jareddilley/LED-Settlers-of-Catan-V2/STL files/Decals/Boat.stl

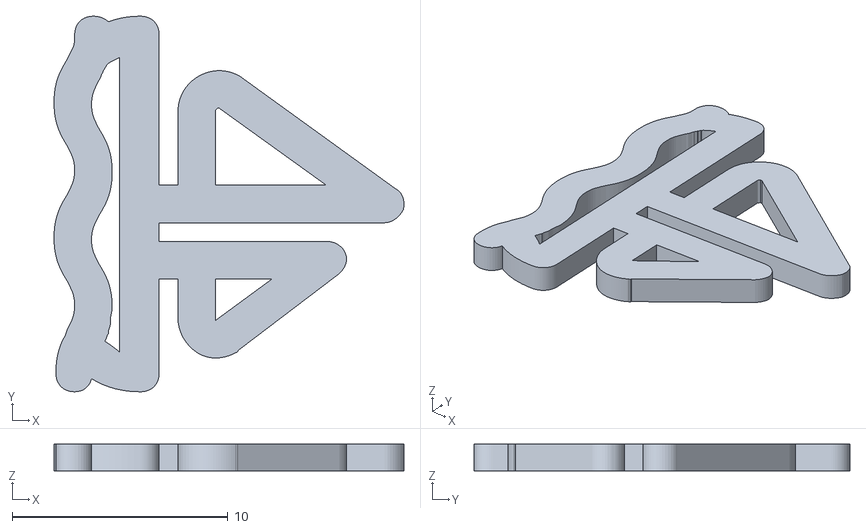
[picture p20: CAD file, 2024-02-23]
STL files/Decals/Boat.stl
16.2 x 17.4 x 1.25
