jareddilley/LED-Settlers-of-Catan-V2/STL files/Boarders/cover-other.stl

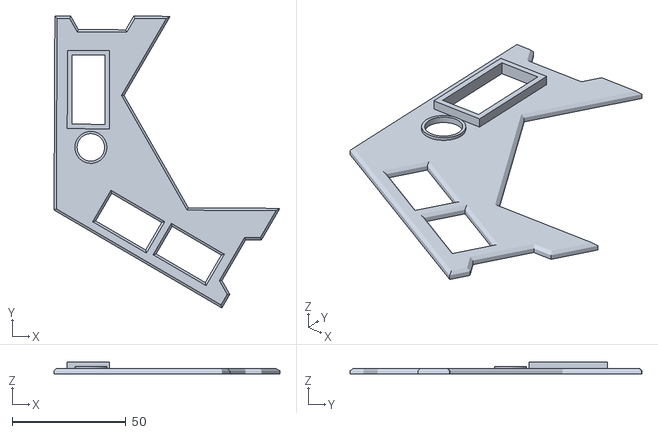
[picture p21: CAD file, 2024-02-23]
STL files/Boarders/cover-other.stl
99.6 x 128.6 x 5.50
