jareddilley/LED-Settlers-of-Catan-V2/STL files/Decals/wheat (1).stl

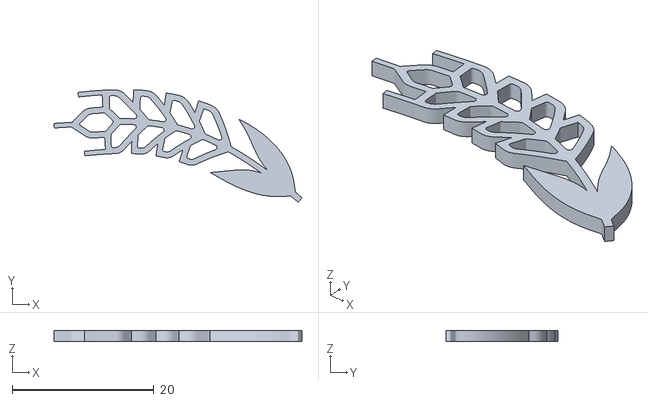
[picture p22: CAD file, 2024-02-23]
STL files/Decals/wheat (1).stl
35.1 x 15.9 x 1.50
