jareddilley/LED-Settlers-of-Catan-V2/STL files/Decals/Port-Diffuser.stl

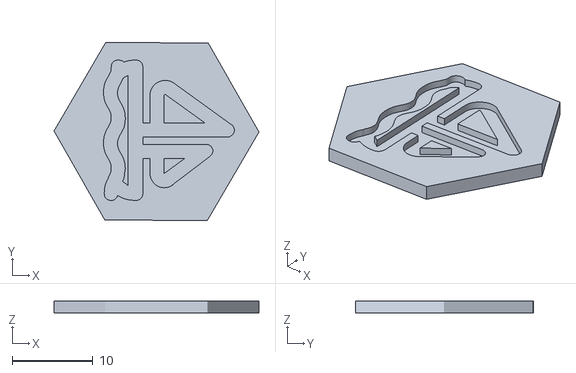
[picture p23: CAD file, 2024-02-23]
STL files/Decals/Port-Diffuser.stl
25.4 x 22.1 x 1.50
