jareddilley/LED-Settlers-of-Catan-V2/STL files/Main Board/1.stl

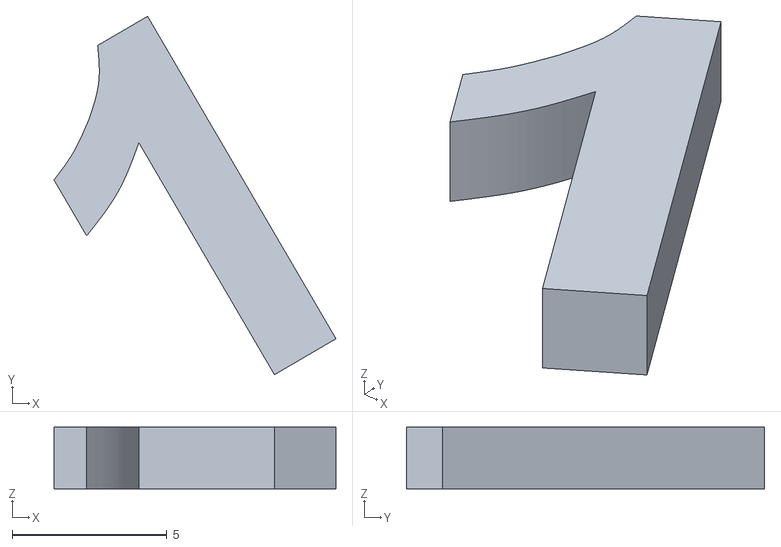
[picture p24: CAD file, 2024-02-23]
STL files/Main Board/1.stl
9.10 x 11.6 x 2.00
