jareddilley/LED-Settlers-of-Catan-V2/STL files/Decals/f.stl

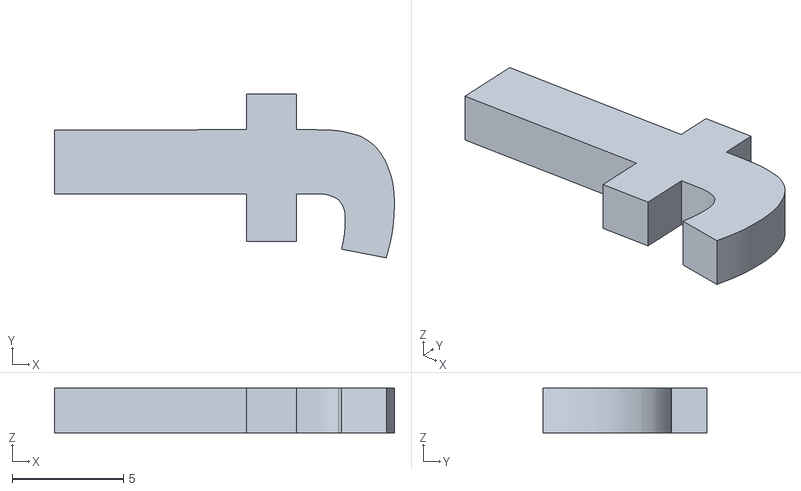
[picture p25: CAD file, 2024-02-23]
STL files/Decals/f.stl
15.3 x 7.35 x 2.00
