jareddilley/LED-Settlers-of-Catan-V2/STL files/Main Board/2-Dot.stl

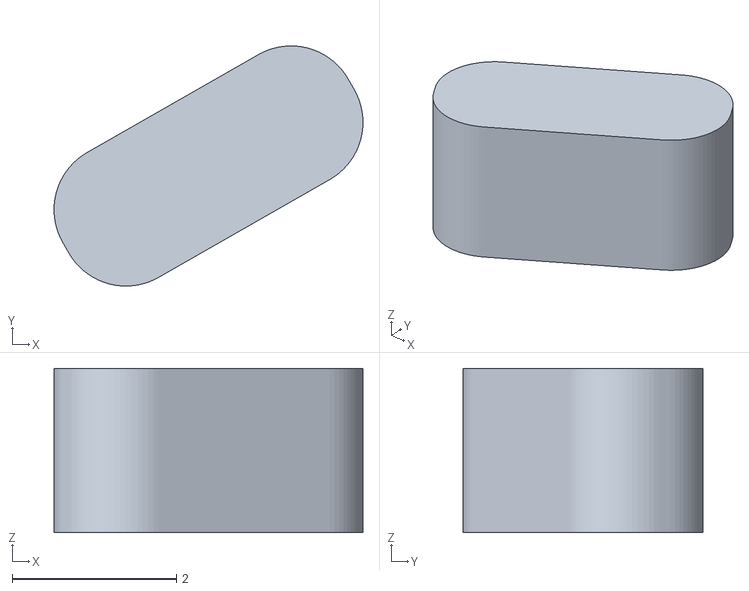
[picture p26: CAD file, 2024-02-23]
STL files/Main Board/2-Dot.stl
3.76 x 2.92 x 2.00
