jareddilley/LED-Settlers-of-Catan-V2/STL files/Boarders/Water-5-other.stl

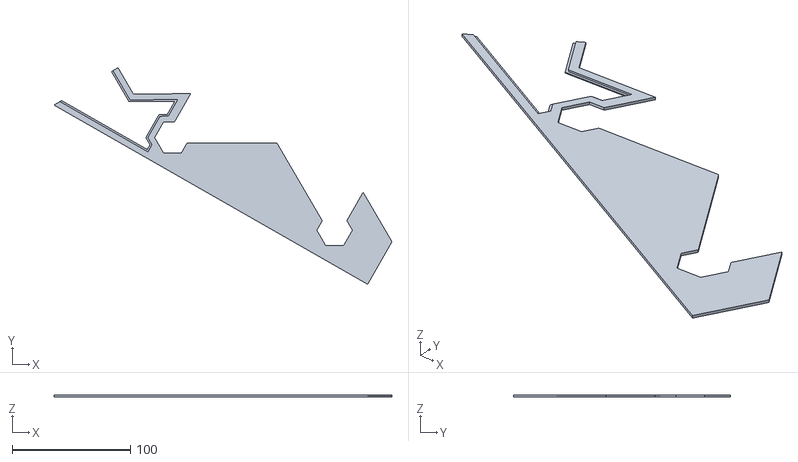
[picture p27: CAD file, 2024-02-23]
STL files/Boarders/Water-5-other.stl
285.5 x 183.0 x 1.50
