jareddilley/LED-Settlers-of-Catan-V2/STL files/Decals/o.stl

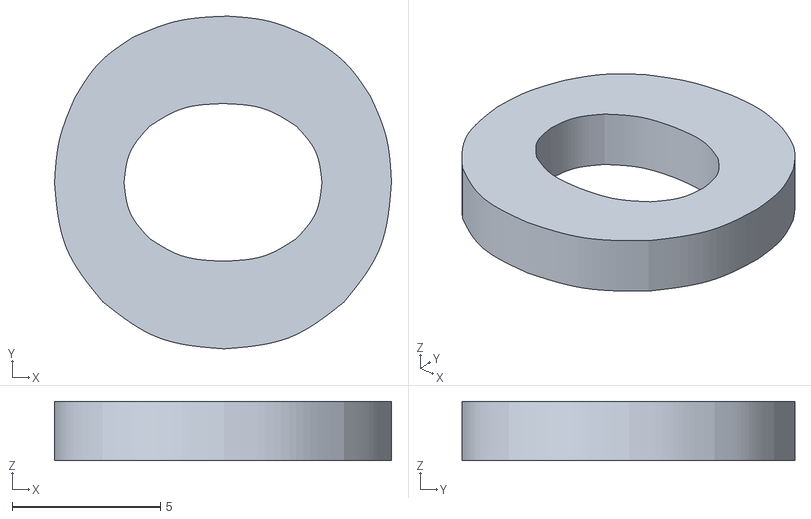
[picture p28: CAD file, 2024-02-23]
STL files/Decals/o.stl
11.4 x 11.2 x 2.00
