jareddilley/LED-Settlers-of-Catan-V2/STL files/Decals/r.stl

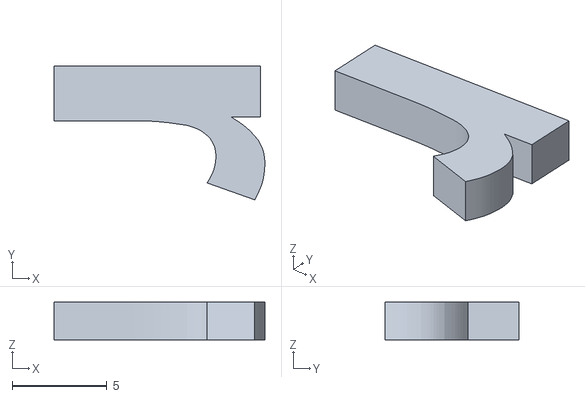
[picture p29: CAD file, 2024-02-23]
STL files/Decals/r.stl
11.1 x 7.04 x 2.00
