jareddilley/LED-Settlers-of-Catan-V2/STL files/Main Board/5-Dot.stl

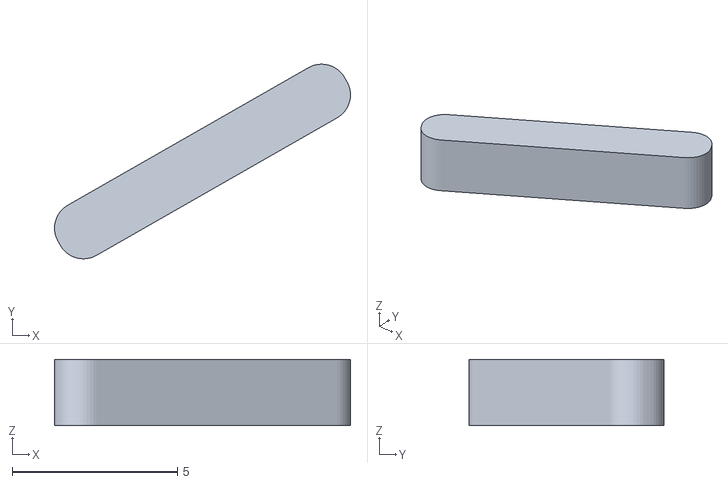
[picture p30: CAD file, 2024-02-23]
STL files/Main Board/5-Dot.stl
8.97 x 5.90 x 2.00
