jareddilley/LED-Settlers-of-Catan-V2/STL files/Decals/n.stl

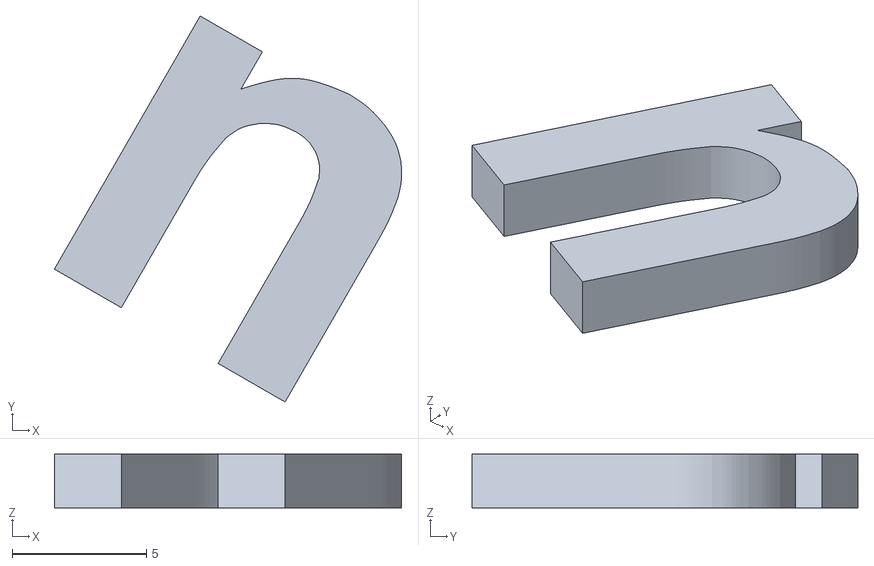
[picture p32: CAD file, 2024-02-23]
STL files/Decals/n.stl
12.9 x 14.4 x 2.00
