jareddilley/LED-Settlers-of-Catan-V2/STL files/Main Board/Base-V2-x6.stl

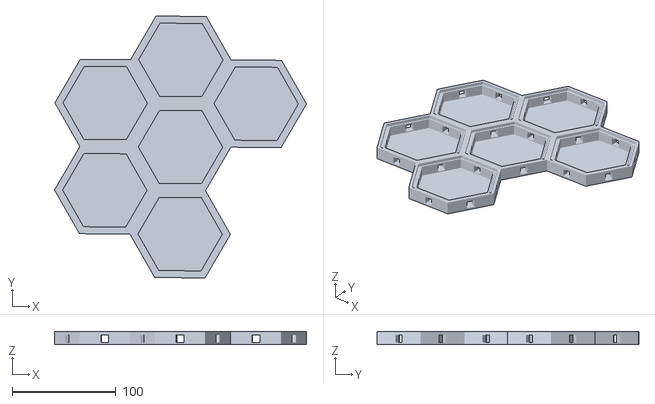
[picture p33: CAD file, 2024-02-23]
STL files/Main Board/Base-V2-x6.stl
242.5 x 251.8 x 12.5
