jareddilley/LED-Settlers-of-Catan-V2/STL files/Decals/sheep (1).stl

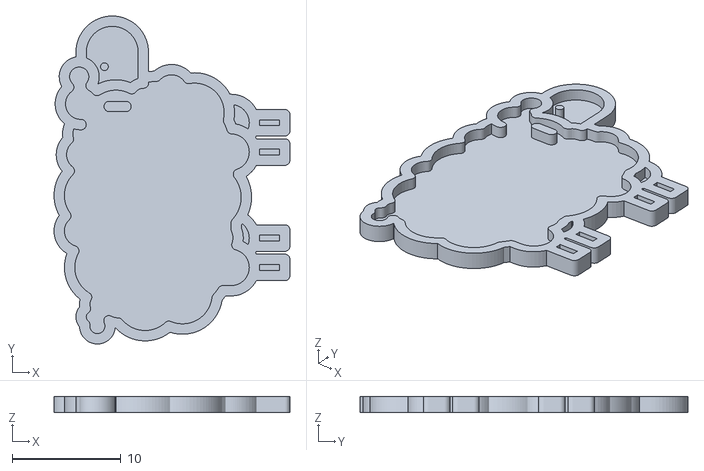
[picture p34: CAD file, 2024-02-23]
STL files/Decals/sheep (1).stl
21.7 x 30.2 x 1.50
