jareddilley/LED-Settlers-of-Catan-V2/STL files/Boarders/Water-2.stl

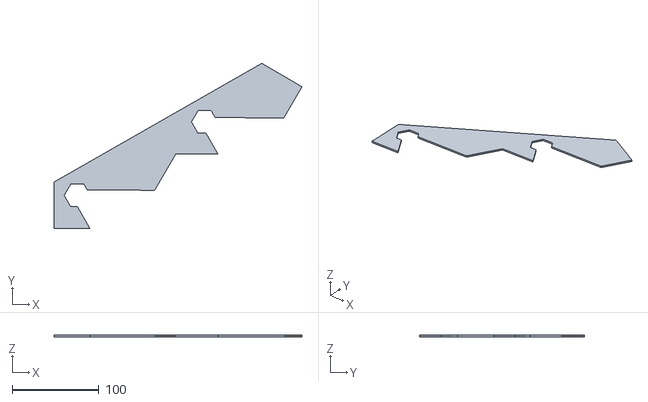
[picture p35: CAD file, 2024-02-23]
STL files/Boarders/Water-2.stl
285.1 x 190.1 x 2.00
