jareddilley/LED-Settlers-of-Catan-V2/STL files/Decals/e.stl

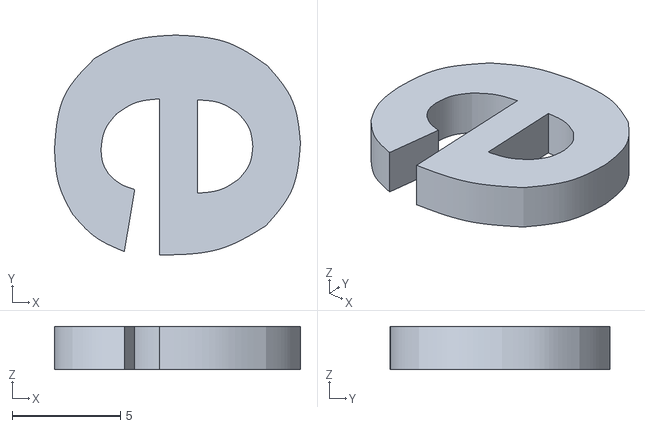
[picture p36: CAD file, 2024-02-23]
STL files/Decals/e.stl
11.4 x 10.2 x 2.00
