jareddilley/LED-Settlers-of-Catan-V2/STL files/Main Board/6.stl

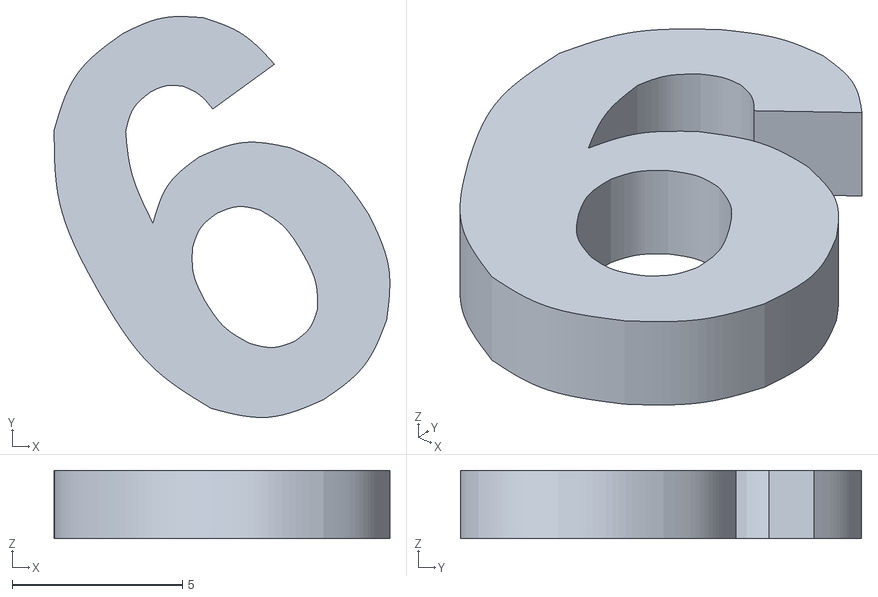
[picture p37: CAD file, 2024-02-23]
STL files/Main Board/6.stl
9.85 x 11.8 x 2.00
