jareddilley/LED-Settlers-of-Catan-V2/STL files/Boarders/Boarder-1.stl

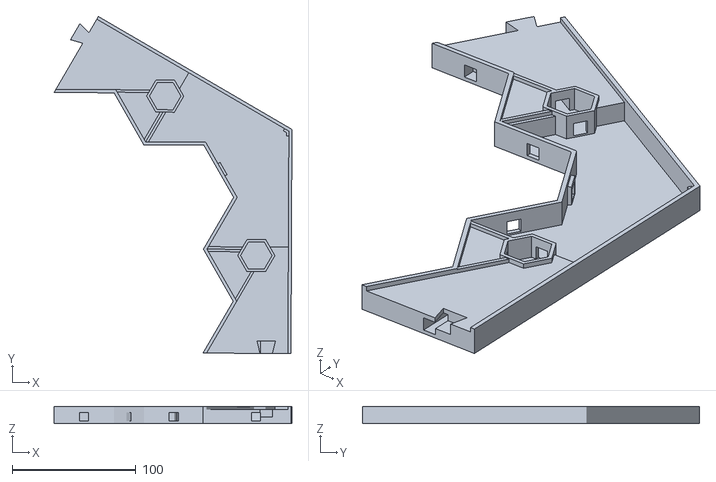
[picture p38: CAD file, 2024-02-23]
STL files/Boarders/Boarder-1.stl
192.0 x 271.9 x 14.0
