jareddilley/LED-Settlers-of-Catan-V2/STL files/Decals/rock (1).stl

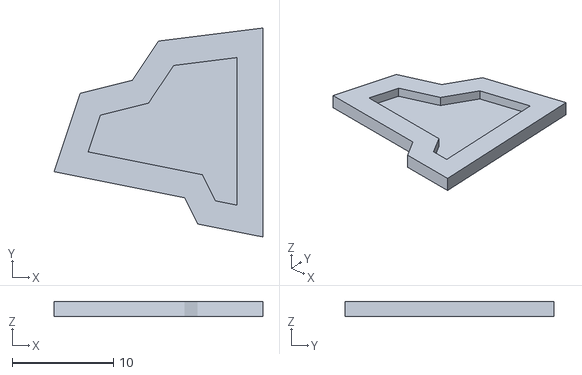
[picture p39: CAD file, 2024-02-23]
STL files/Decals/rock (1).stl
20.6 x 20.6 x 1.50
