jareddilley/LED-Settlers-of-Catan-V2/STL files/Main Board/5.stl

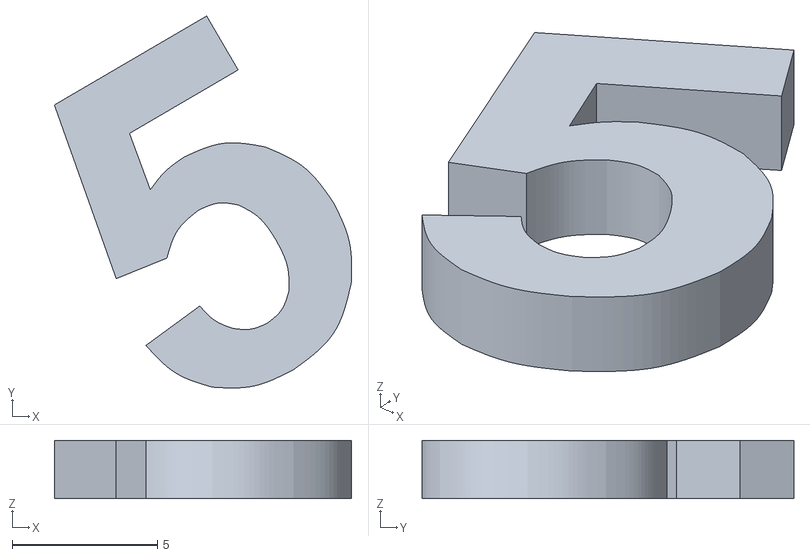
[picture p40: CAD file, 2024-02-23]
STL files/Main Board/5.stl
10.3 x 12.8 x 2.00
