jareddilley/LED-Settlers-of-Catan-V2/STL files/Boarders/Water-6 (1)-other.stl

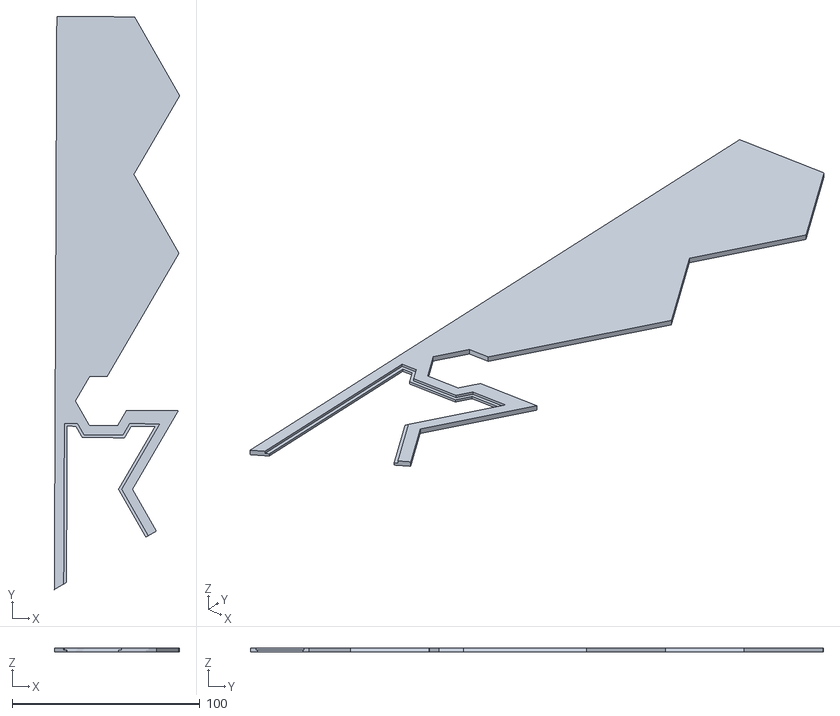
[picture p41: CAD file, 2024-02-23]
STL files/Boarders/Water-6 (1)-other.stl
66.8 x 305.2 x 2.00
