jareddilley/LED-Settlers-of-Catan-V2/STL files/Decals/brick (1).stl

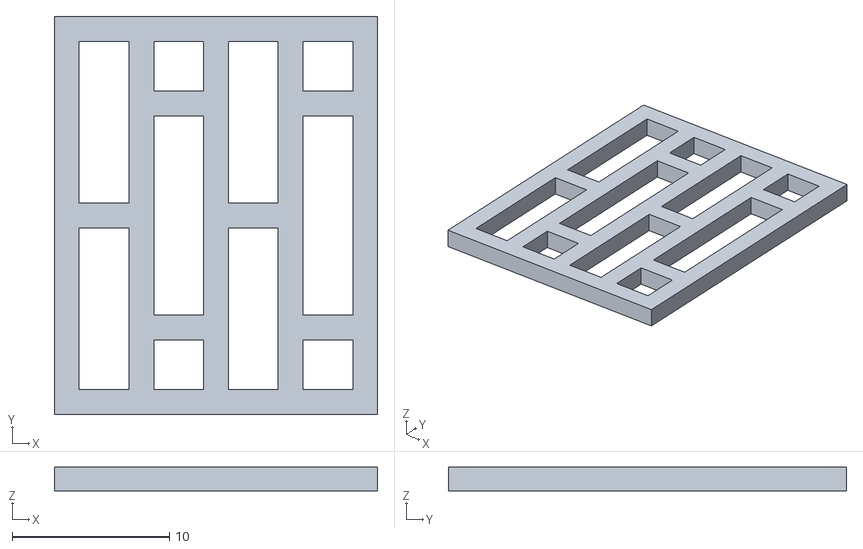
[picture p42: CAD file, 2024-02-23]
STL files/Decals/brick (1).stl
20.6 x 25.3 x 1.50
