jareddilley/LED-Settlers-of-Catan-V2/STL files/Main Board/2.stl

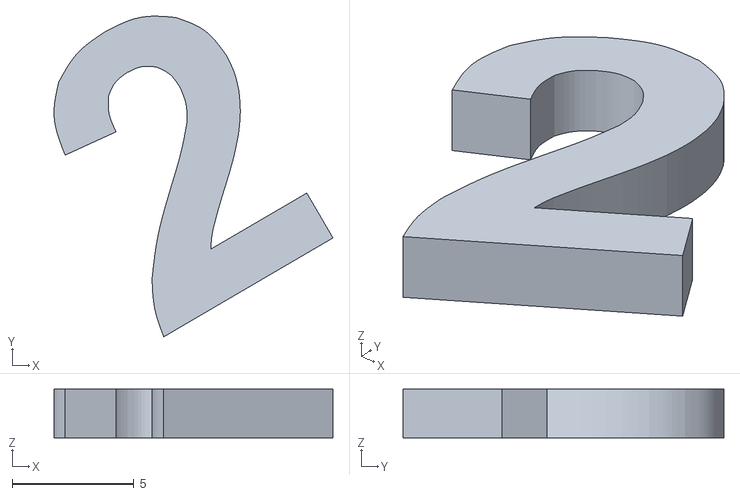
[picture p43: CAD file, 2024-02-23]
STL files/Main Board/2.stl
11.5 x 13.2 x 2.00
