jareddilley/LED-Settlers-of-Catan-V2/STL files/Decals/a.stl

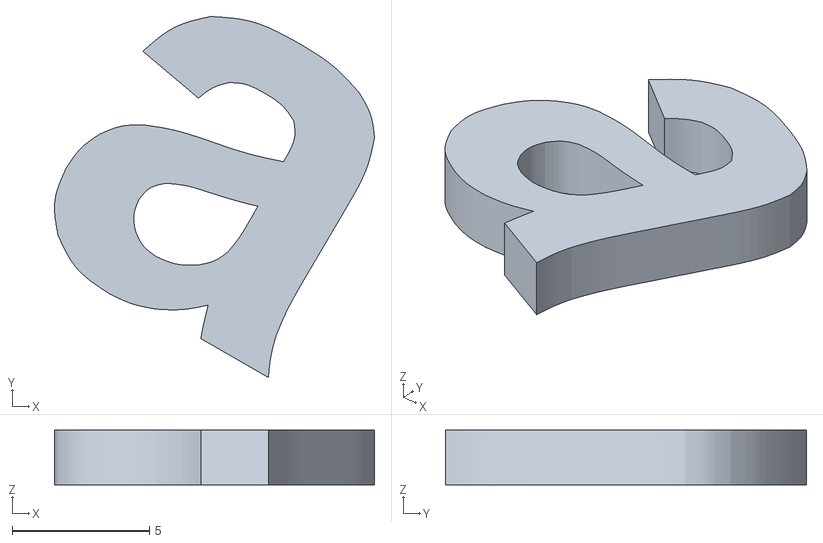
[picture p44: CAD file, 2024-02-23]
STL files/Decals/a.stl
11.7 x 13.2 x 2.00
