jareddilley/LED-Settlers-of-Catan-V2/STL files/Main Board/Connector.stl

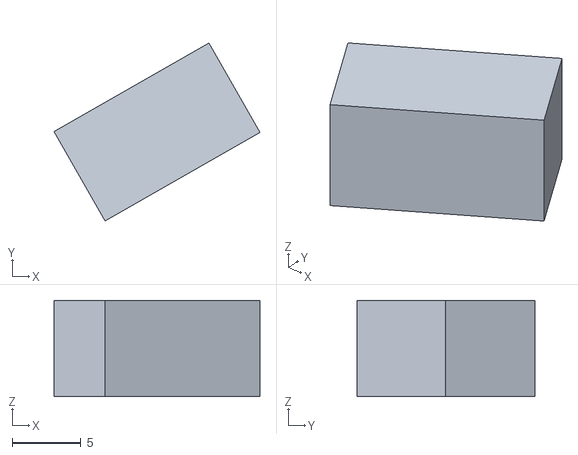
[picture p45: CAD file, 2024-02-23]
STL files/Main Board/Connector.stl
15.0 x 13.0 x 7.00
