jareddilley/LED-Settlers-of-Catan-V2/STL files/Boarders/Boarder-3.stl

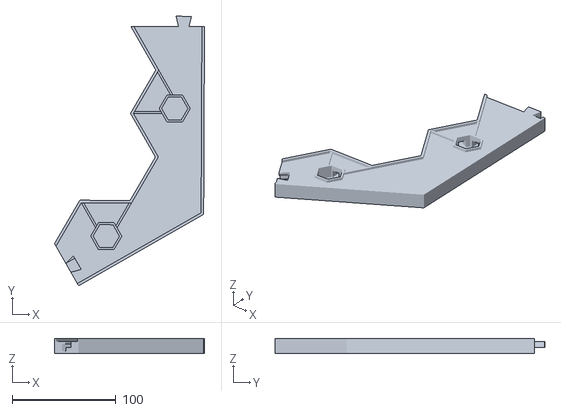
[picture p46: CAD file, 2024-02-23]
STL files/Boarders/Boarder-3.stl
144.6 x 259.8 x 14.0
