jareddilley/LED-Settlers-of-Catan-V2/STL files/Decals/s.stl

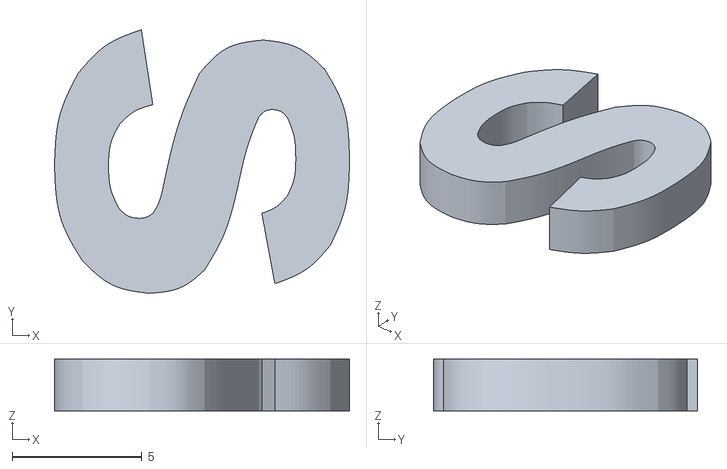
[picture p47: CAD file, 2024-02-23]
STL files/Decals/s.stl
11.4 x 10.1 x 2.00
