jareddilley/LED-Settlers-of-Catan-V2/STL files/Main Board/Base-V2-x5.stl

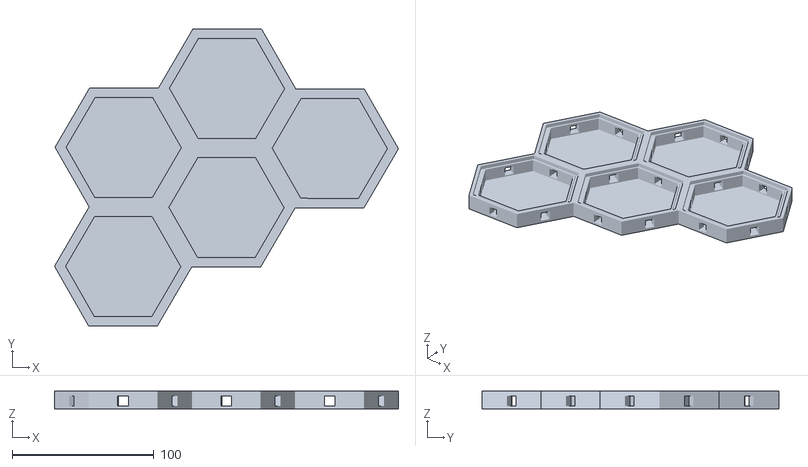
[picture p48: CAD file, 2024-02-23]
STL files/Main Board/Base-V2-x5.stl
242.5 x 209.6 x 12.5
