jareddilley/LED-Settlers-of-Catan-V2/STL files/Boarders/Water-4.stl

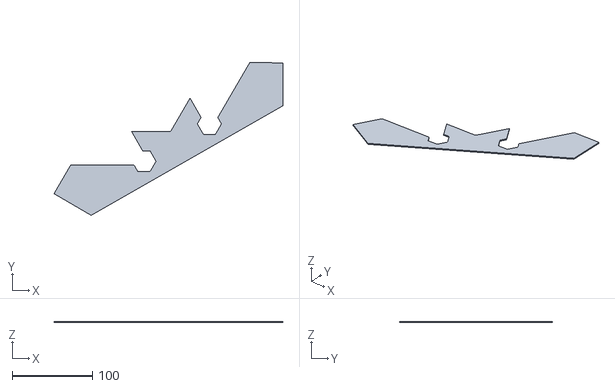
[picture p49: CAD file, 2024-02-23]
STL files/Boarders/Water-4.stl
285.1 x 190.1 x 1.50
