jareddilley/LED-Settlers-of-Catan-V2/STL files/Decals/t.stl

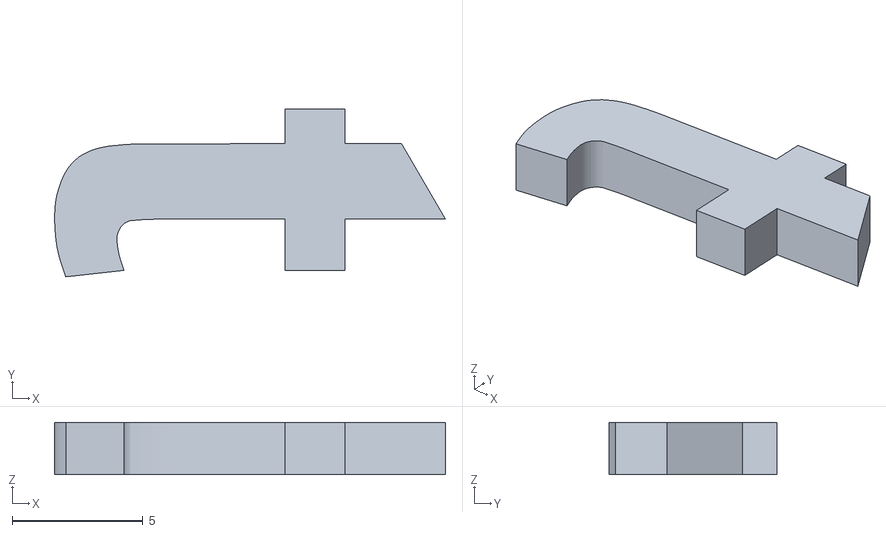
[picture p50: CAD file, 2024-02-23]
STL files/Decals/t.stl
14.9 x 6.41 x 2.00
