jareddilley/LED-Settlers-of-Catan-V2/STL files/Decals/Settlers of.stl

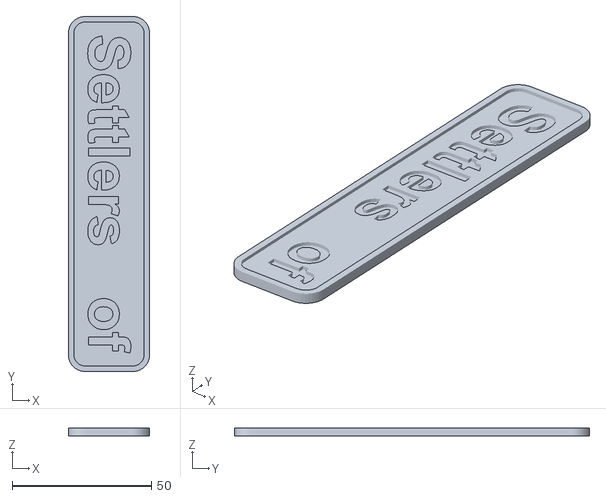
[picture p51: CAD file, 2024-02-23]
STL files/Decals/Settlers of.stl
29.2 x 127.7 x 3.00
