jareddilley/LED-Settlers-of-Catan-V2/STL files/Main Board/4.stl

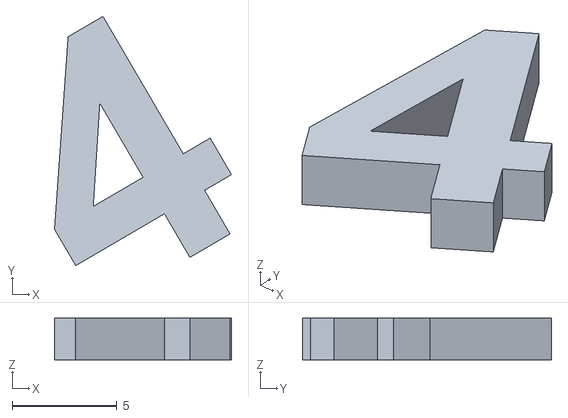
[picture p52: CAD file, 2024-02-23]
STL files/Main Board/4.stl
8.46 x 11.9 x 2.00
