jareddilley/LED-Settlers-of-Catan-V2/STL files/Main Board/8.stl

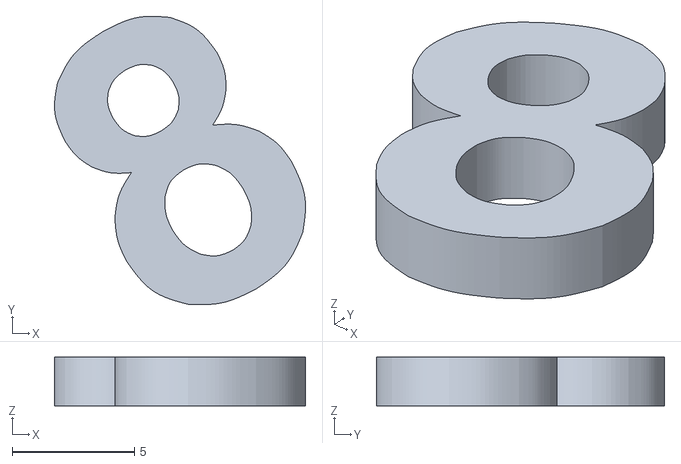
[picture p53: CAD file, 2024-02-23]
STL files/Main Board/8.stl
10.3 x 11.8 x 2.00
