jareddilley/LED-Settlers-of-Catan-V2/STL files/Main Board/3-Dot.stl

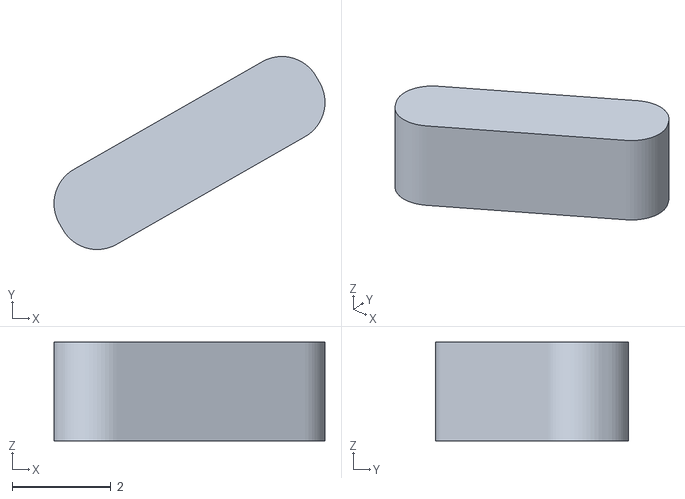
[picture p54: CAD file, 2024-02-23]
STL files/Main Board/3-Dot.stl
5.49 x 3.91 x 2.00
