jareddilley/LED-Settlers-of-Catan-V2/STL files/Main Board/0.stl

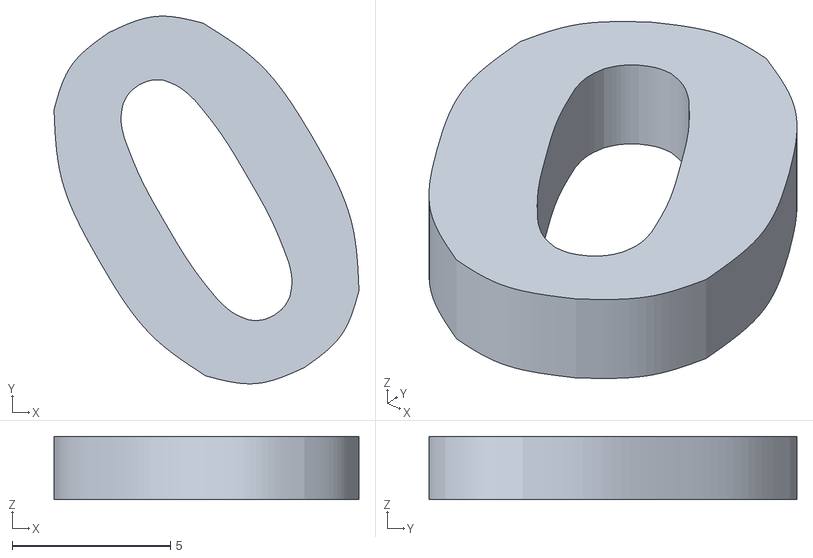
[picture p55: CAD file, 2024-02-23]
STL files/Main Board/0.stl
9.64 x 11.6 x 2.00
