jareddilley/LED-Settlers-of-Catan-V2/STL files/Main Board/7.stl

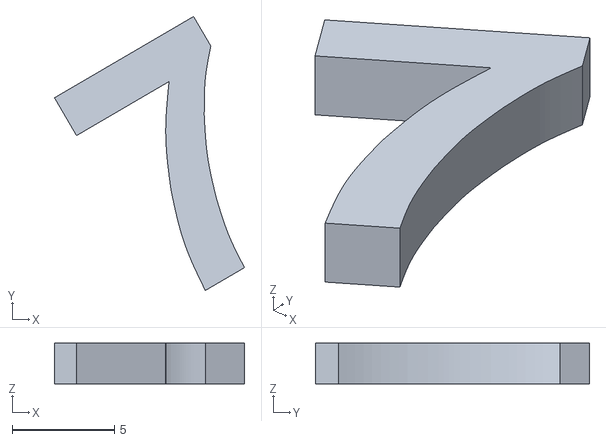
[picture p56: CAD file, 2024-02-23]
STL files/Main Board/7.stl
9.28 x 13.4 x 2.00
